Multi-EAR/Multi-EAR/Casing/Small/small_top.png

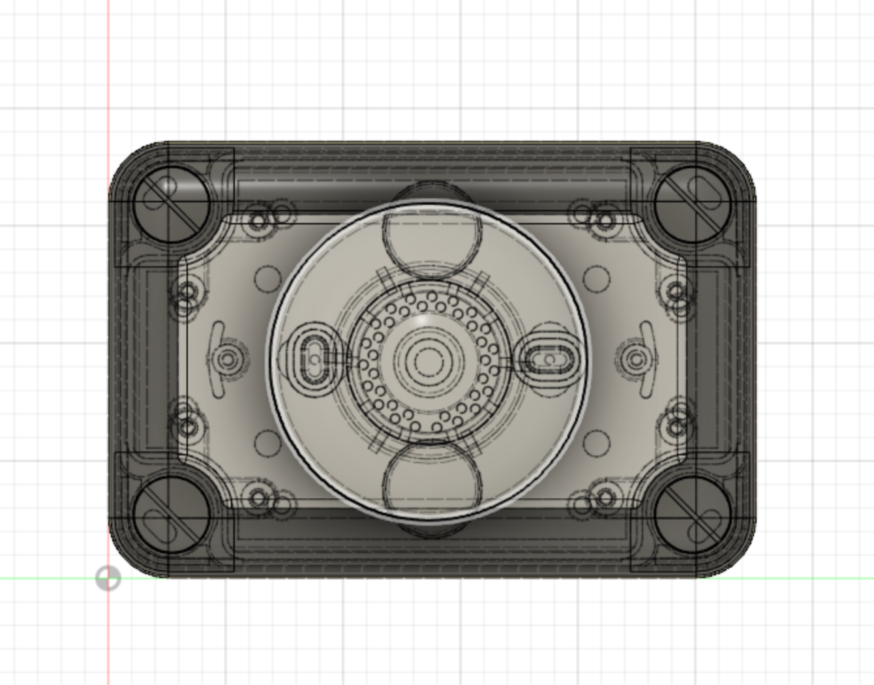
Casing/Small/small_top.png
